kwiecinski/Hotair-and-soldering-iron-station/docs/datasheets/Buzzer BCE.png

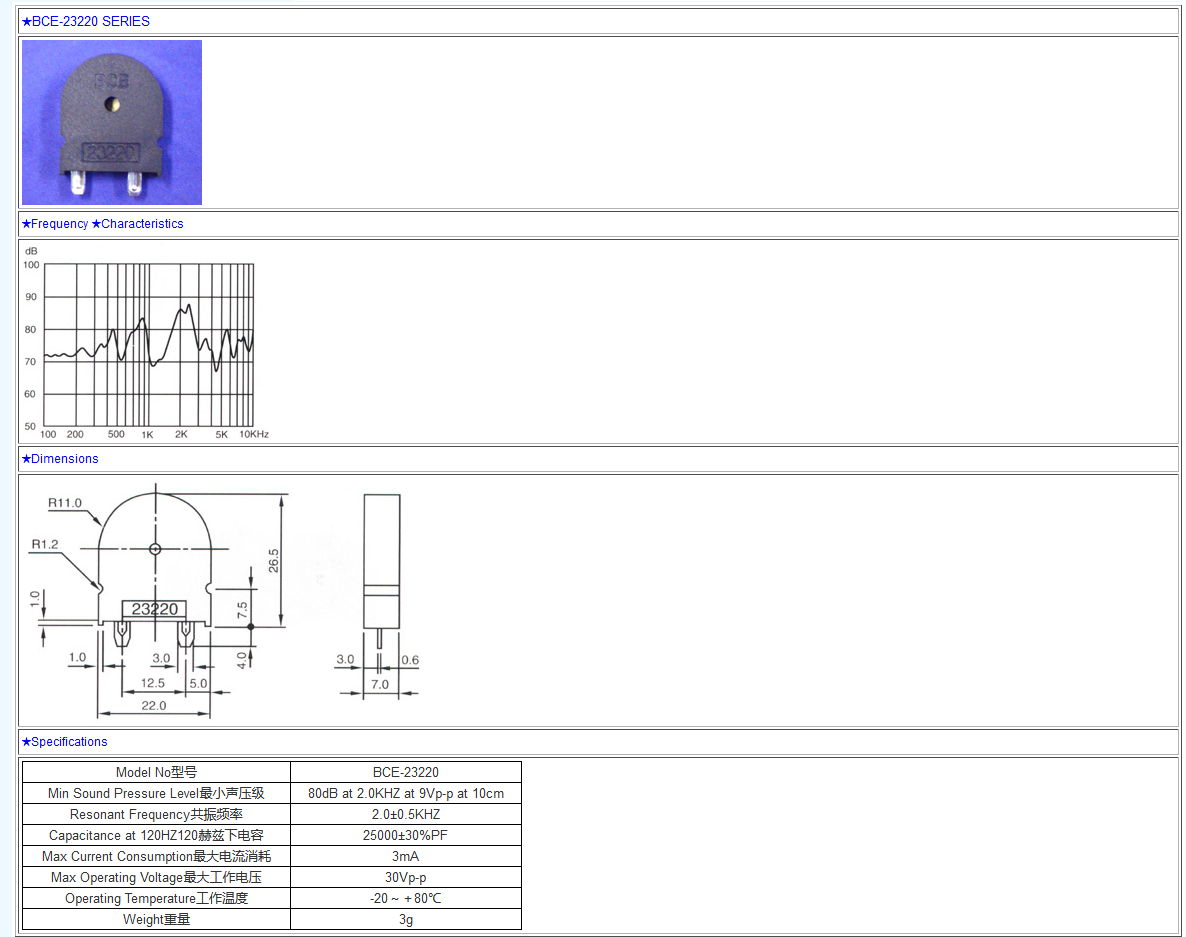
docs/datasheets/Buzzer BCE.png
