kwiecinski/Hotair-and-soldering-iron-station/docs/photos/front_panel_2.jpg

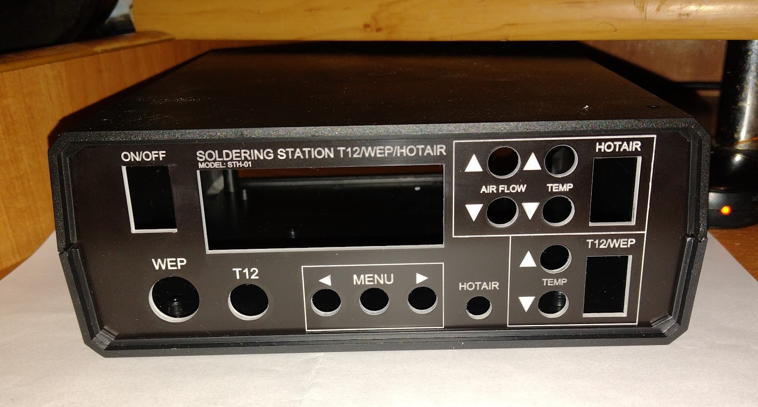
docs/photos/front_panel_2.jpg
