kwiecinski/Hotair-and-soldering-iron-station/docs/photos/PCB-matufacture/PCB_termotransfer_bottom.jpg

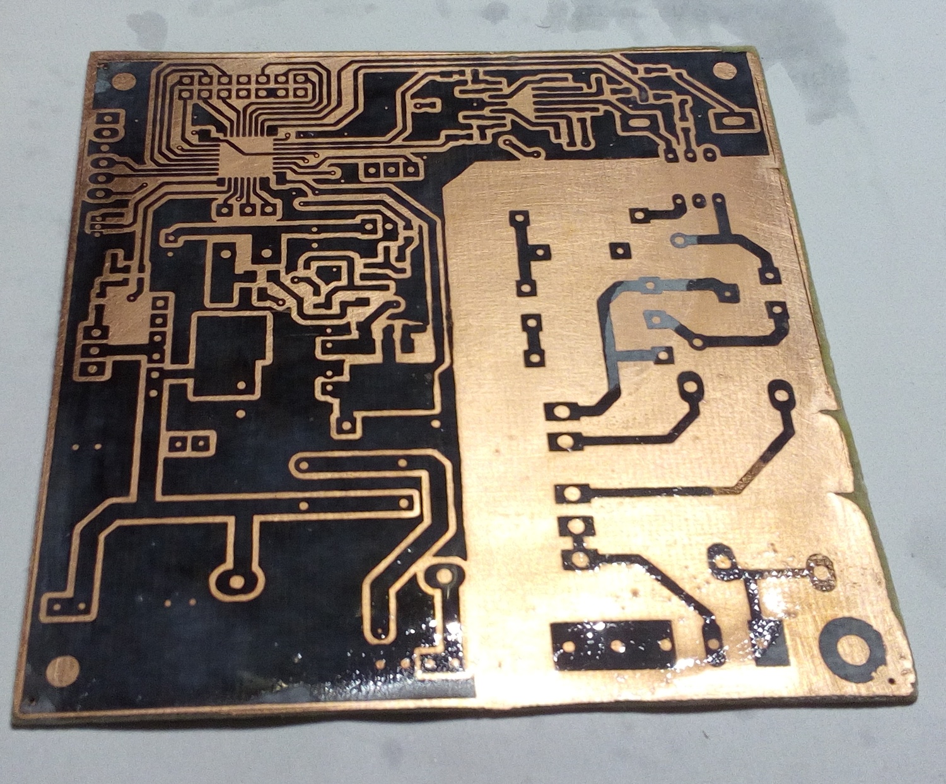
docs/photos/PCB-matufacture/PCB_termotransfer_bottom.jpg
