kwiecinski/Hotair-and-soldering-iron-station/case/3D Print Models/JPG/cable latch.jpg

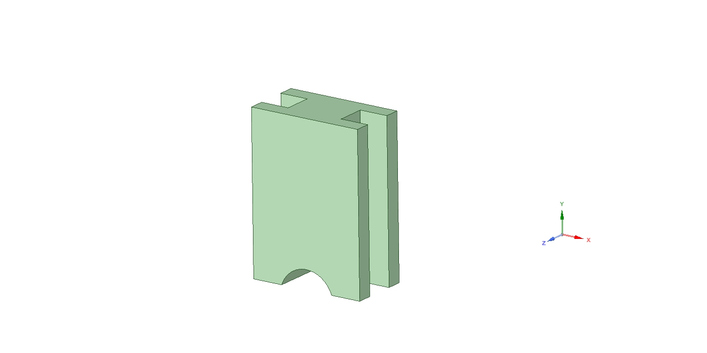
case/3D Print Models/JPG/cable latch.jpg
