kwiecinski/Hotair-and-soldering-iron-station/case/3D Print Models/JPG/SMPS case.jpg

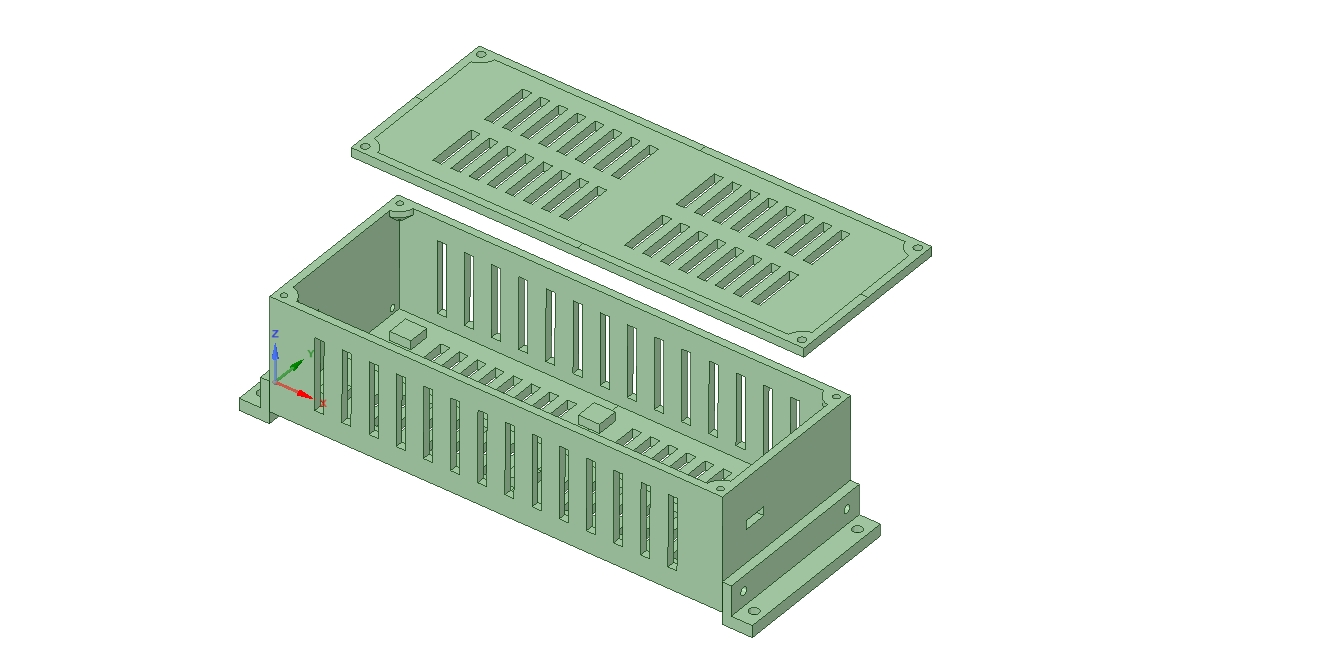
case/3D Print Models/JPG/SMPS case.jpg
