kwiecinski/Hotair-and-soldering-iron-station/code/Core/Inc/adc_functions.h

/*
 * fan_regulator.h
 *
 *  Created on: 6 sty 2021
 */

#ifndef INC_ADC_FUNCTIONS_H_
#define INC_ADC_FUNCTIONS_H_

#ifdef __cplusplus
extern "C" {
#endif

#define FAN_ADC_INPUT		1
#define HOTAIR_ADC_INPUT	2
#define T12_ADC_INPUT		3
#define TEMP_SNS_ADC_INPUT	4


void Init_ADC(void);
float ADC_Read_Voltage(uint8_t adc_input);

#ifdef __cplusplus
}
#endif

#endif /* INC_ADC_FUNCTIONS_H_ */
